moritzsalla/cci-physcomp-final/journal/log-01/scan-013.png

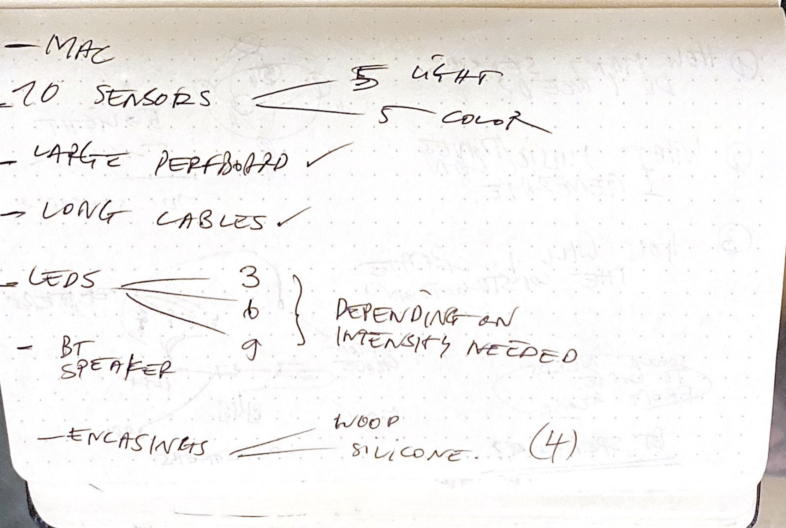
journal/log-01/scan-013.png
