moritzsalla/cci-physcomp-final/journal/log-03/screenshot-3.png

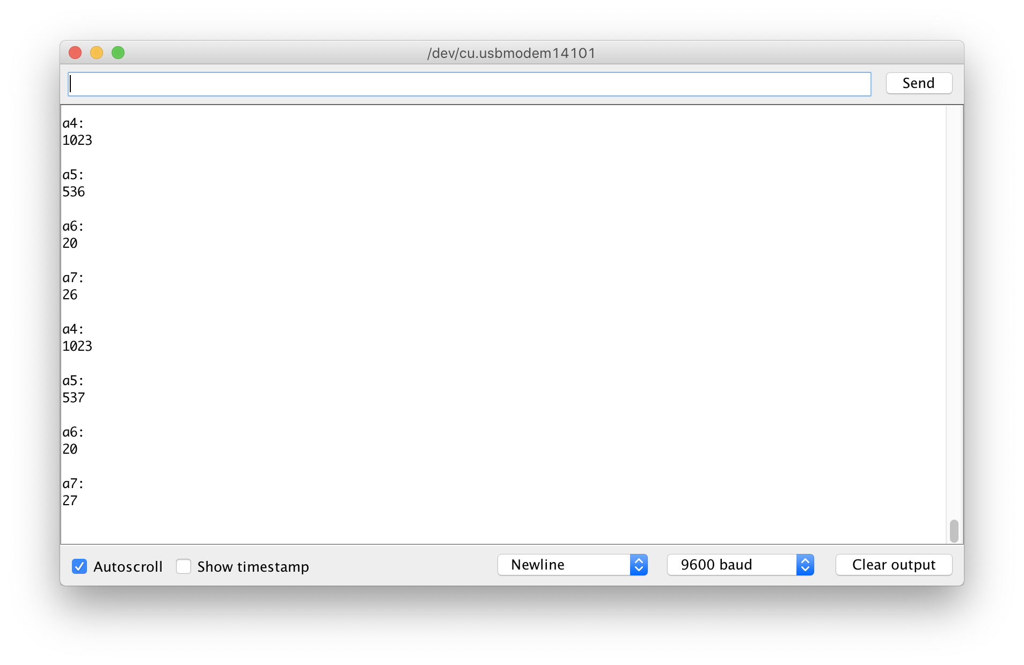
journal/log-03/screenshot-3.png
