moritzsalla/cci-physcomp-final/journal/log-04/Bildschirmfoto 2019-12-06 um 18.15.19.png

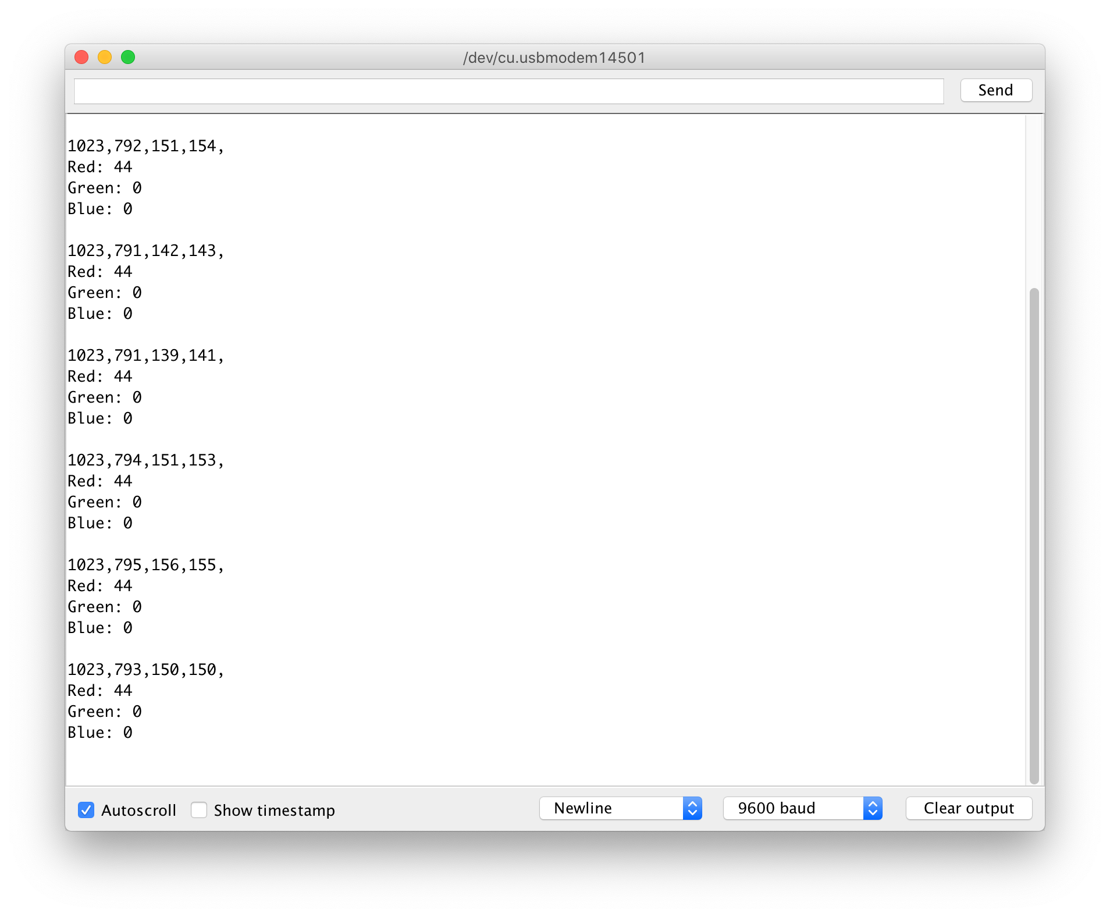
journal/log-04/Bildschirmfoto 2019-12-06 um 18.15.19.png
