moritzsalla/cci-physcomp-final/journal/log-05/image-09.jpeg

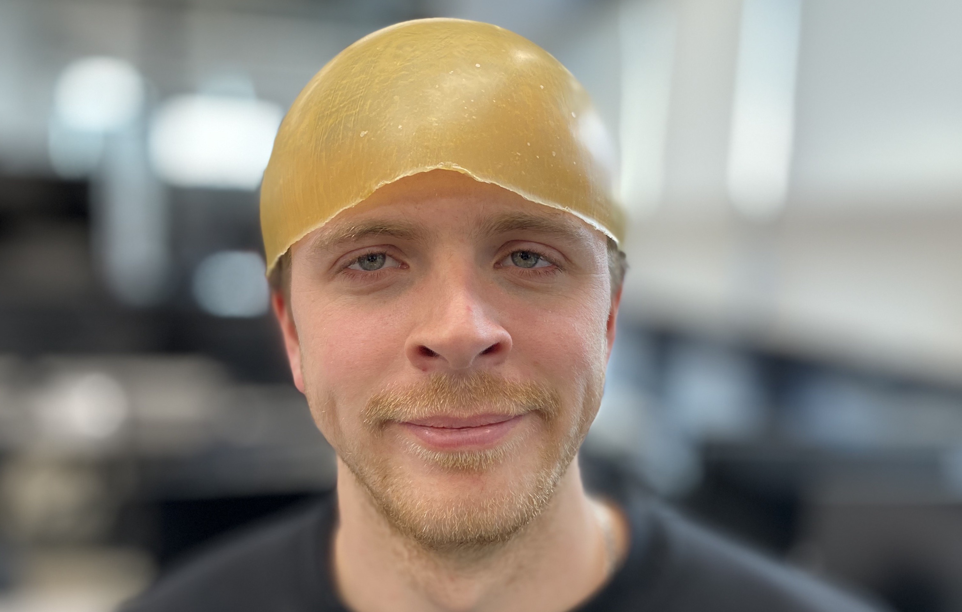
journal/log-05/image-09.jpeg
