moritzsalla/cci-physcomp-final/journal/log-05/image-12.jpeg

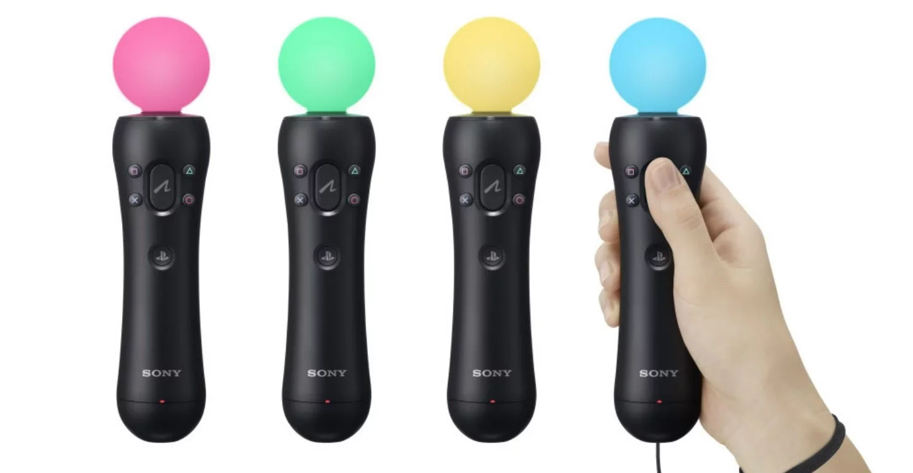
journal/log-05/image-12.jpeg
