moritzsalla/cci-physcomp-final/code/theremin/calibration.ino

void initialize() {
  // initialize color sensors through softwire lib
  RGB_sensor_1.init(39, 38);
  RGB_sensor_2.init(37, 36);
  RGB_sensor_3.init(35, 34);
  RGB_sensor_4.init(33, 32);
}

void calibrate() {
  while (millis() < 2000) {
    // read photoresistors
    photo1in = analogRead(photo1pin);
    photo2in = analogRead(photo2pin);
    photo3in = analogRead(photo3pin);
    photo4in = analogRead(photo4pin);

    // calculate average
    photoValue = (analogRead(photo1pin) + analogRead(photo2pin) + analogRead(photo3pin) + analogRead(photo4pin)) / 4;

    // record minimum sensor value
    if (photoValue < photoMin) {
      photoMin = photoValue;
    }

    // record maximum sensor value
    if (colorValue < colorMin) {
      colorMin = colorValue;
    }
  }
}
